JoeyByrnes/Tello_Joint_Encoder/firmware/Core/Src/fdcan.c

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
/* Includes ------------------------------------------------------------------*/
#include "fdcan.h"

FDCAN_HandleTypeDef hfdcan1;

/* FDCAN1 init function */
void MX_FDCAN1_Init(void)
{

  hfdcan1.Instance = FDCAN1;
  hfdcan1.Init.ClockDivider = FDCAN_CLOCK_DIV1;
  hfdcan1.Init.FrameFormat = FDCAN_FRAME_CLASSIC;
  hfdcan1.Init.Mode = FDCAN_MODE_NORMAL;
  hfdcan1.Init.AutoRetransmission = DISABLE;
  hfdcan1.Init.TransmitPause = DISABLE;
  hfdcan1.Init.ProtocolException = DISABLE;
  hfdcan1.Init.NominalPrescaler = 34;
  hfdcan1.Init.NominalSyncJumpWidth = 1;
  hfdcan1.Init.NominalTimeSeg1 = 2;
  hfdcan1.Init.NominalTimeSeg2 = 2;
  hfdcan1.Init.DataPrescaler = 1;
  hfdcan1.Init.DataSyncJumpWidth = 1;
  hfdcan1.Init.DataTimeSeg1 = 1;
  hfdcan1.Init.DataTimeSeg2 = 1;
  hfdcan1.Init.StdFiltersNbr = 0;
  hfdcan1.Init.ExtFiltersNbr = 0;
  hfdcan1.Init.TxFifoQueueMode = FDCAN_TX_FIFO_OPERATION;
  if (HAL_FDCAN_Init(&hfdcan1) != HAL_OK)
  {
    Error_Handler();
  }
}

void HAL_FDCAN_MspInit(FDCAN_HandleTypeDef* fdcanHandle)
{

  GPIO_InitTypeDef GPIO_InitStruct = {0};
  RCC_PeriphCLKInitTypeDef PeriphClkInit = {0};
  if(fdcanHandle->Instance==FDCAN1)
  {
  /** Initializes the peripherals clocks
  */
    PeriphClkInit.PeriphClockSelection = RCC_PERIPHCLK_FDCAN;
    PeriphClkInit.FdcanClockSelection = RCC_FDCANCLKSOURCE_PCLK1;
    if (HAL_RCCEx_PeriphCLKConfig(&PeriphClkInit) != HAL_OK)
    {
      Error_Handler();
    }

    /* FDCAN1 clock enable */
    __HAL_RCC_FDCAN_CLK_ENABLE();

    __HAL_RCC_GPIOA_CLK_ENABLE();
    /**FDCAN1 GPIO Configuration
    PA11     ------> FDCAN1_RX
    PA12     ------> FDCAN1_TX
    */
    GPIO_InitStruct.Pin = GPIO_PIN_11|GPIO_PIN_12;
    GPIO_InitStruct.Mode = GPIO_MODE_AF_PP;
    GPIO_InitStruct.Pull = GPIO_NOPULL;
    GPIO_InitStruct.Speed = GPIO_SPEED_FREQ_LOW;
    GPIO_InitStruct.Alternate = GPIO_AF9_FDCAN1;
    HAL_GPIO_Init(GPIOA, &GPIO_InitStruct);

    /* FDCAN1 interrupt Init */
    HAL_NVIC_SetPriority(FDCAN1_IT0_IRQn, 0, 0);
    HAL_NVIC_EnableIRQ(FDCAN1_IT0_IRQn);
  }
}

void HAL_FDCAN_MspDeInit(FDCAN_HandleTypeDef* fdcanHandle)
{

  if(fdcanHandle->Instance==FDCAN1)
  {
    /* Peripheral clock disable */
    __HAL_RCC_FDCAN_CLK_DISABLE();

    /**FDCAN1 GPIO Configuration
    PA11     ------> FDCAN1_RX
    PA12     ------> FDCAN1_TX
    */
    HAL_GPIO_DeInit(GPIOA, GPIO_PIN_11|GPIO_PIN_12);

    /* FDCAN1 interrupt Deinit */
    HAL_NVIC_DisableIRQ(FDCAN1_IT0_IRQn);
  }
}

/* USER CODE BEGIN 1 */
//
//void can_rx_init(CANRxMessage *msg){
//
//	msg->filter.IdType = FDCAN_STANDARD_ID;
//	msg->filter.FilterIndex = 0;
//	msg->filter.FilterType = FDCAN_FILTER_MASK;
//	msg->filter.FilterConfig = FDCAN_FILTER_TO_RXFIFO0;
//	msg->filter.FilterID1 = CAN_ID;
//	msg->filter.FilterID2 = 0x7FF;
//
//	if (HAL_FDCAN_ConfigFilter(&CAN_H, &msg->filter) != HAL_OK)
//	{
//		Error_Handler();
//	}
//
////	if (HAL_FDCAN_ConfigGlobalFilter(&CAN_H, FDCAN_REJECT, FDCAN_REJECT, FDCAN_FILTER_REMOTE, FDCAN_FILTER_REMOTE) != HAL_OK)
////	{
////		Error_Handler();
////	}
//
//}
//
//void can_tx_init(CANTxMessage *msg){
//
//	msg->tx_header.Identifier = CAN_MASTER;
//	msg->tx_header.IdType = FDCAN_STANDARD_ID;
//	msg->tx_header.TxFrameType = FDCAN_DATA_FRAME;
//	msg->tx_header.DataLength = FDCAN_DLC_BYTES_6;
//	msg->tx_header.ErrorStateIndicator = FDCAN_ESI_ACTIVE;
//	msg->tx_header.BitRateSwitch = FDCAN_BRS_OFF;
//	msg->tx_header.FDFormat = FDCAN_CLASSIC_CAN;
//	msg->tx_header.TxEventFifoControl = FDCAN_NO_TX_EVENTS;
//	msg->tx_header.MessageMarker = 0;
//
//}
//
///// CAN Reply Packet Structure ///
///// 16 bit position, between -4*pi and 4*pi
///// 12 bit velocity, between -30 and + 30 rad/s
///// 12 bit current, between -40 and 40;
///// CAN Packet is 5 8-bit words
///// Formatted as follows.  For each quantity, bit 0 is LSB
///// 0: [position[15-8]]
///// 1: [position[7-0]]
///// 2: [velocity[11-4]]
///// 3: [velocity[3-0], current[11-8]]
///// 4: [current[7-0]]
//void pack_reply(CANTxMessage *msg, uint8_t id, float p, float v, float t){
//    int p_int = float_to_uint(p, P_MIN, P_MAX, 16);
//    int v_int = float_to_uint(v, V_MIN, V_MAX, 12);
//    int t_int = float_to_uint(t, -I_MAX*KT*GR, I_MAX*KT*GR, 12);
//    msg->data[0] = id;
//    msg->data[1] = p_int>>8;
//    msg->data[2] = p_int&0xFF;
//    msg->data[3] = v_int>>4;
//    msg->data[4] = ((v_int&0xF)<<4) + (t_int>>8);
//    msg->data[5] = t_int&0xFF;
//    }
//

/* USER CODE END 1 */
