JoeyByrnes/Tello_Joint_Encoder/firmware/Core/Inc/dwt_delay.hpp

/*
 * Simple microseconds delay routine, utilizing ARM's DWT
 * (Data Watchpoint and Trace Unit) and HAL library.
 * Intended to use with gcc compiler, but I hope it can be used
 * with any other C compiler across the Universe (provided that
 * ARM and CMSIS already invented) :)
 * Max K
 *
 *
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
 * us_delay is distributed in the hope that it will be useful,
 * but WITHOUT ANY WARRANTY; without even the implied warranty
 * of MERCHANTABILITY or FITNESS FOR A PARTICULAR PURPOSE. See
 * the GNU General Public License for more details.
 * http://www.gnu.org/licenses/.
 */

#include <stdint.h>

#ifndef INC_DWT_DELAY_H_
#define INC_DWT_DELAY_H_

#define DWT_DELAY_NEWBIE 0

#ifdef __cplusplus
extern "C"
{
#endif


void DWT_Init(void);
void DWT_Delay(uint32_t us);

#ifdef __cplusplus
}
#endif

#endif /* INC_DWT_DELAY_DWT_DELAY_H_ */
